ElectronicCats/DAP-Cat-Programmer/firmware/CMSIS_DAP/src/CMSIS_DAPusb/USBHID.h

#ifndef __USB_HID_H__
#define __USB_HID_H__

#include <stdint.h>
#include "include/ch554.h"
#include "include/ch554_usb.h"

#ifdef __cplusplus
extern "C" {
#endif

void USBInit(void);

#ifdef __cplusplus
} // extern "C"
#endif

#endif
